amuhak/hackgt-26/src/buoy/sensors.h

#pragma once
#include "proto.h"

namespace sensors {
void begin();
// Call every loop: feeds the GPS parser and samples the IMU at 50 Hz.
void poll();
// Fills the sensor fields of `r` and resets the per-period wave statistics.
void fill(Record& r);
// Bytes received from the GPS so far; 0 means it's miswired or unpowered.
uint32_t gpsChars();
// A full batch of 50 Hz IMU samples (header left for the mesh to fill), if one is ready.
bool takeMotion(MotionMsg& out, size_t& n);
#ifdef DEBUG_LOG
// Prints every sensor's current reading; call about once a second.
void debugTick();
#endif
}  // namespace sensors
