amuhak/hackgt-26/tools/collector.py

#!/usr/bin/env python3
"""Laptop side of the buoy mesh: drains the collector ESP32 into SQLite.

    python tools/collector.py COM6 [--db buoy.db]

On connect it tells the collector what the DB already has, so buoys only send
what's new, then acks each batch once committed so buoys can free flash.

Only records contiguous with what the DB has are stored and acked. A corrupt
line or a jump in seq sends REWIND, and the collector resends from the last
ACKs. A jump that persists after a rewind is real (the mesh evicted those
records) and is accepted.

Live IMU frames (MOT lines, 50 Hz accel + gyro from buoys in direct range of
the collector) go into the `motion` table with an orientation estimate for 3D
rendering. They are best effort: never acked, resent or relayed.
"""
import argparse
from collections import deque
import math
import sqlite3
import struct
import sys
import time
import zlib

import serial

# Mirrors struct Record in include/proto.h (42 bytes, little-endian, packed).
RECORD_FMT = "<IIIIiihhIHHhhBB"
assert struct.calcsize(RECORD_FMT) == 42

F_BMP_OK, F_IMU_OK, F_WATER_OK, F_GPS_FIX, F_GPS_TIME, F_SIM = 1, 2, 4, 8, 16, 128

SCHEMA = """
CREATE TABLE IF NOT EXISTS readings (
  origin        TEXT    NOT NULL,  -- buoy id (low 4 bytes of MAC, hex)
  seq           INTEGER NOT NULL,
  gps_time      INTEGER,           -- unix seconds from GPS, NULL without a GPS time
  uptime_s      INTEGER,
  lat           REAL,
  lon           REAL,
  water_temp_c  REAL,
  air_temp_c    REAL,
  pressure_hpa  REAL,
  wave_rms_g    REAL,              -- vertical accel RMS over the sample period
  wave_peak_g   REAL,
  pitch_deg     REAL,
  roll_deg      REAL,
  sats          INTEGER,
  flags         INTEGER,
  received_at   INTEGER NOT NULL,  -- laptop unix time
  PRIMARY KEY (origin, seq)
);
CREATE TABLE IF NOT EXISTS motion (
  origin       TEXT    NOT NULL,
  t_ms         INTEGER NOT NULL,   -- buoy clock (ms since boot); samples are 20 ms apart
  received_at  REAL    NOT NULL,   -- laptop unix time the frame arrived
  ax_g REAL, ay_g REAL, az_g REAL,             -- buoy axes: x forward, y left, z up
  gx_dps REAL, gy_dps REAL, gz_dps REAL,
  qw REAL, qx REAL, qy REAL, qz REAL,          -- orientation, buoy -> world
  roll_deg REAL, pitch_deg REAL, yaw_deg REAL  -- yaw drifts: there's no magnetometer
);
CREATE INDEX IF NOT EXISTS motion_by_time ON motion (origin, received_at);
"""

# Mirrors struct MotionMsg: header, t0_ms, period_ms, then 6 x int16 per sample.
MOTION_HDR = "<BBBBIIH"
MOTION_SAMPLE = "<6h"
ACCEL_LSB_PER_G, GYRO_LSB_PER_DPS = 8192.0, 65.5
assert struct.calcsize(MOTION_HDR) == 14 and struct.calcsize(MOTION_SAMPLE) == 12


def decode(raw: bytes, now: int) -> tuple:
    (origin, seq, gps_time, uptime, lat, lon, water, air, pressure,
     rms, peak, pitch, roll, sats, flags) = struct.unpack(RECORD_FMT, raw)
    fix = flags & F_GPS_FIX
    return (
        f"{origin:08x}", seq,
        gps_time if flags & F_GPS_TIME else None, uptime,
        lat / 1e7 if fix else None, lon / 1e7 if fix else None,
        water / 100 if flags & F_WATER_OK else None,
        air / 100 if flags & F_BMP_OK else None,
        pressure / 100 if flags & F_BMP_OK else None,
        rms / 1000 if flags & F_IMU_OK else None,
        peak / 1000 if flags & F_IMU_OK else None,
        pitch / 100 if flags & F_IMU_OK else None,
        roll / 100 if flags & F_IMU_OK else None,
        sats, flags, now,
    )


class Orientation:
    """Mahony filter: integrates the gyro and pulls tilt toward the gravity
    direction the accelerometer sees. Quaternion is (w, x, y, z), buoy -> world.

    Gravity can't correct yaw, so a gyro bias turns into steady spin. The buoy
    only calibrates at boot, and skips it if it was moving then (~2 deg/s of
    bias on #1), so the bias is re-measured here whenever the buoy sits still."""

    KP = 0.5  # how hard the accelerometer corrects the gyro (1/s)
    STILL_N = 50  # 1 s window at 50 Hz
    STILL_GYRO_DPS = 1.0  # per-axis spread in the window that counts as still
    STILL_ACCEL_G = 0.03

    def __init__(self):
        self.q = None
        self.t_ms = None
        self.bias = [0.0, 0.0, 0.0]  # deg/s, on top of the buoy's boot calibration
        self.win = deque(maxlen=self.STILL_N)

    def learn_bias(self, a, g_dps):
        self.win.append((math.sqrt(a[0] ** 2 + a[1] ** 2 + a[2] ** 2), *g_dps))
        if len(self.win) < self.STILL_N:
            return
        cols = list(zip(*self.win))
        if max(cols[0]) - min(cols[0]) > self.STILL_ACCEL_G:
            return
        if any(max(c) - min(c) > self.STILL_GYRO_DPS for c in cols[1:]):
            return
        self.bias = [sum(c) / len(c) for c in cols[1:]]

    @staticmethod
    def from_accel(a):
        roll = math.atan2(a[1], a[2])
        pitch = math.atan2(-a[0], math.hypot(a[1], a[2]))
        cr, sr, cp, sp = math.cos(roll / 2), math.sin(roll / 2), math.cos(pitch / 2), math.sin(pitch / 2)
        return (cr * cp, sr * cp, cr * sp, -sr * sp)

    def update(self, t_ms, a, g_dps):
        if self.t_ms is not None and t_ms < self.t_ms:  # buoy rebooted: new boot calibration
            self.bias = [0.0, 0.0, 0.0]
        if self.q is None or not 0 < t_ms - self.t_ms <= 1000:
            self.q = self.from_accel(a)  # first sample, or after a gap / reboot
            self.win.clear()
        else:
            dt = (t_ms - self.t_ms) / 1000
            self.learn_bias(a, g_dps)
            w, x, y, z = self.q
            gx, gy, gz = (math.radians(v - b) for v, b in zip(g_dps, self.bias))
            n = math.sqrt(a[0] ** 2 + a[1] ** 2 + a[2] ** 2)
            if n > 0:
                ax, ay, az = (v / n for v in a)
                vx, vy, vz = 2 * (x * z - w * y), 2 * (w * x + y * z), w * w - x * x - y * y + z * z
                gx += self.KP * (ay * vz - az * vy)
                gy += self.KP * (az * vx - ax * vz)
                gz += self.KP * (ax * vy - ay * vx)
            w, x, y, z = (w + 0.5 * dt * (-x * gx - y * gy - z * gz),
                          x + 0.5 * dt * (w * gx + y * gz - z * gy),
                          y + 0.5 * dt * (w * gy - x * gz + z * gx),
                          z + 0.5 * dt * (w * gz + x * gy - y * gx))
            n = math.sqrt(w * w + x * x + y * y + z * z)
            self.q = (w / n, x / n, y / n, z / n)
        self.t_ms = t_ms
        return self.q

    @staticmethod
    def euler(q):
        w, x, y, z = q
        roll = math.atan2(2 * (w * x + y * z), 1 - 2 * (x * x + y * y))
        pitch = math.asin(max(-1.0, min(1.0, 2 * (w * y - z * x))))
        yaw = math.atan2(2 * (w * z + x * y), 1 - 2 * (y * y + z * z))
        return math.degrees(roll), math.degrees(pitch), math.degrees(yaw)


def parse_mot(line: str):
    """(origin, t0_ms, period_ms, samples) from a MOT line, or None if garbled."""
    parts = line.split()
    try:
        raw = bytes.fromhex(parts[1])
        if len(parts) != 3 or len(raw) < 14 or zlib.crc32(raw) != int(parts[2], 16):
            return None
        _, _, _, count, sender, t0, period = struct.unpack_from(MOTION_HDR, raw)
        if len(raw) != 14 + 12 * count:
            return None
    except (ValueError, IndexError, struct.error):
        return None
    samples = [struct.unpack_from(MOTION_SAMPLE, raw, 14 + 12 * i) for i in range(count)]
    return f"{sender:08x}", t0, period, samples


def motion_rows(frame, filters: dict, now: float) -> list:
    origin, t0, period, samples = frame
    f = filters.setdefault(origin, Orientation())
    rows = []
    for i, s in enumerate(samples):
        t = t0 + i * period
        a = [v / ACCEL_LSB_PER_G for v in s[:3]]
        g = [v / GYRO_LSB_PER_DPS for v in s[3:]]
        q = f.update(t, a, g)
        rows.append((origin, t, now, *a, *g, *q, *Orientation.euler(q)))
    return rows


def send(ser: serial.Serial, line: str) -> None:
    ser.write((line + "\n").encode())


REWIND_TIMEOUT_S = 5  # resend REWIND if the collector never confirms it


def start_session(ser: serial.Serial, db: sqlite3.Connection) -> dict:
    """Returns origin -> next expected seq."""
    rows = db.execute("SELECT origin, MAX(seq) + 1 FROM readings GROUP BY origin").fetchall()
    for origin, nxt in rows:
        send(ser, f"HAVE {origin} {nxt}")
    send(ser, "START")
    log(f"collector ready; DB has {len(rows)} buoys")
    return dict(rows)


def parse_rec(line: str):
    """The raw record from a REC line, or None if it's garbled."""
    parts = line.split()
    try:
        raw = bytes.fromhex(parts[1])
        if len(raw) != 42 or len(parts) != 3 or zlib.crc32(raw) != int(parts[2], 16):
            return None
    except (ValueError, IndexError):
        return None
    return raw


def log(msg: str) -> None:
    print(f"{time.strftime('%H:%M:%S')} {msg}", flush=True)


def run_session(ser: serial.Serial, db: sqlite3.Connection) -> None:
    """Drains one serial connection until it errors out."""
    # Opening the port usually resets the ESP32, which then says READY. If it
    # didn't reset, it's already running, so announce ourselves right away too.
    time.sleep(1.5)
    expect = start_session(ser, db)  # origin -> next seq we'll store
    started = time.monotonic()
    pending = set()  # origins to ack after commit
    jump_ok = {}  # origin -> gap start we already rewound for
    rewind_sent = None  # REWIND awaiting the collector's confirmation
    new_rows = 0
    last_flush = time.monotonic()
    filters = {}  # origin -> Orientation
    motion_count = {}  # origin -> samples since the last motion log line
    last_motion_log = time.monotonic()
    motion_dirty = False

    def rewind(why: str) -> None:
        nonlocal rewind_sent
        send(ser, "REWIND")
        rewind_sent = time.monotonic()
        log(f"rewind: {why}")

    while True:
        line = ser.readline().decode(errors="replace").strip()
        if rewind_sent and time.monotonic() - rewind_sent > REWIND_TIMEOUT_S:
            rewind("no confirmation")
        if line.startswith("READY") and time.monotonic() - started > 3:
            expect = start_session(ser, db)  # collector rebooted
            started = time.monotonic()
        elif line.startswith("LOG rewound"):
            rewind_sent = None  # REC lines from here on follow the rewind
        elif line.startswith("REC "):
            if rewind_sent:
                continue  # sent before the collector rewound
            raw = parse_rec(line)
            if raw is None:
                rewind("corrupt line")
                continue
            row = decode(raw, int(time.time()))
            origin, seq = row[0], row[1]
            e = expect.get(origin, 0)
            if seq > e:
                if jump_ok.get(origin) != e:
                    jump_ok[origin] = e
                    rewind(f"{origin} jumped {e} -> {seq}")
                    continue
                log(f"{origin}: records {e}..{seq - 1} no longer exist in the mesh; skipping")
            cur = db.execute(f"INSERT OR IGNORE INTO readings VALUES ({','.join('?' * len(row))})", row)
            new_rows += cur.rowcount
            if seq >= e:
                expect[origin] = seq + 1
                pending.add(origin)
        elif line.startswith("MOT "):
            frame = parse_mot(line)
            if frame:
                rows = motion_rows(frame, filters, time.time())
                db.executemany(f"INSERT INTO motion VALUES ({','.join('?' * len(rows[0]))})", rows)
                motion_count[frame[0]] = motion_count.get(frame[0], 0) + len(rows)
                motion_dirty = True
        elif line.startswith("LOG "):
            log("collector: " + line[4:])

        if motion_count and time.monotonic() - last_motion_log > 10:
            log("motion: " + ", ".join(f"{o} {n} samples" for o, n in sorted(motion_count.items())))
            motion_count.clear()
            last_motion_log = time.monotonic()
        if motion_dirty and not pending and time.monotonic() - last_flush > 0.5:
            db.commit()  # live view: motion rows show up within 0.5 s
            motion_dirty = False
            last_flush = time.monotonic()
        if pending and time.monotonic() - last_flush > 0.5:
            db.commit()
            motion_dirty = False
            for origin in pending:
                send(ser, f"ACK {origin} {expect[origin]}")
            counts = ", ".join(f"{o} up to #{expect[o] - 1}" for o in sorted(pending))
            log(f"+{new_rows} new ({counts})")
            pending.clear()
            new_rows = 0
            last_flush = time.monotonic()


def main() -> None:
    ap = argparse.ArgumentParser(description=__doc__, formatter_class=argparse.RawDescriptionHelpFormatter)
    ap.add_argument("port", help="collector serial port, e.g. COM6 or /dev/ttyUSB0")
    ap.add_argument("--db", default="buoy.db")
    ap.add_argument("--baud", type=int, default=921600)
    args = ap.parse_args()

    db = sqlite3.connect(args.db)
    db.execute("PRAGMA journal_mode=WAL")  # the web backend reads while we write
    db.executescript(SCHEMA)
    log(f"waiting for collector on {args.port}...")
    try:
        while True:  # survive unplug/replug of the collector
            try:
                with serial.Serial(args.port, args.baud, timeout=0.2) as ser:
                    run_session(ser, db)
            except serial.SerialException as e:
                db.commit()
                log(f"serial error ({e}); retrying")
                time.sleep(2)
    except KeyboardInterrupt:
        pass
    finally:
        db.commit()
        db.close()


if __name__ == "__main__":
    sys.exit(main())
